Adrian256256/Proiect-TSC/Images/Image_1.png

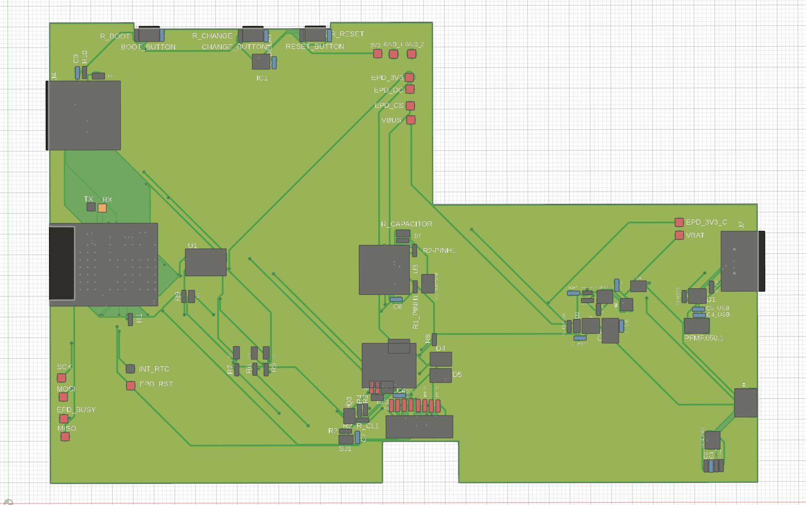
Images/Image_1.png
