Adrian256256/Proiect-TSC/Images/Image_2.png

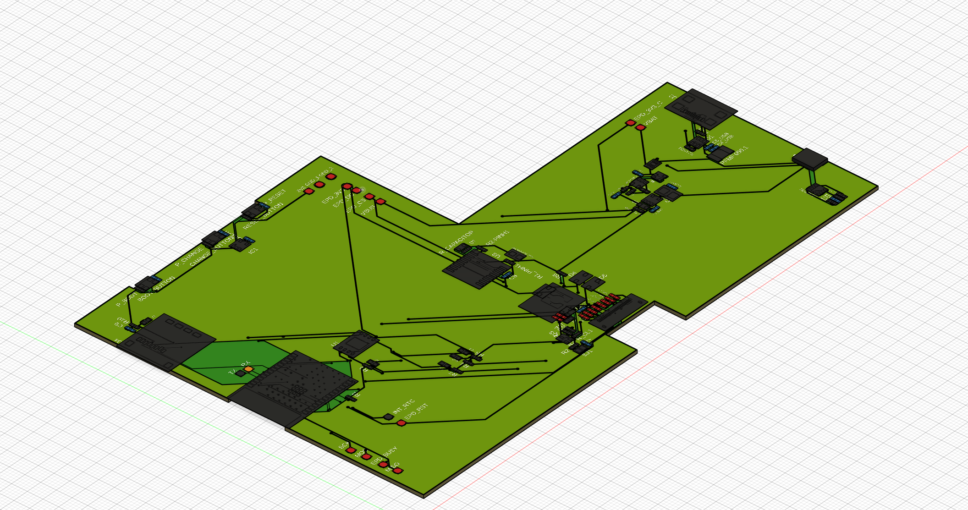
Images/Image_2.png
