Adrian256256/Proiect-TSC/Images/Image_3.png

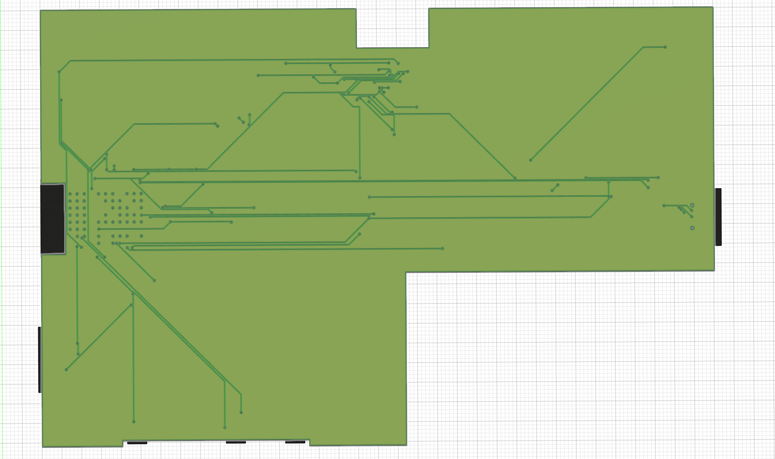
Images/Image_3.png
