Adrian256256/Proiect-TSC/Images/Image_4.png

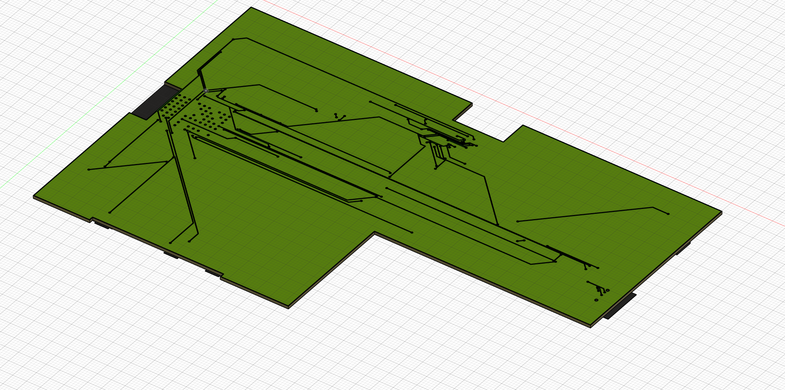
Images/Image_4.png
