Adrian256256/Proiect-TSC/Images/Image_5.png

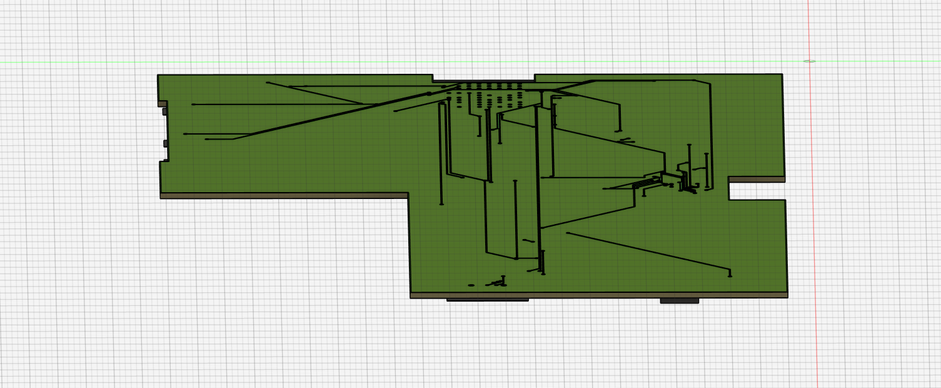
Images/Image_5.png
